syvrc/syvrcboard-v0/PCB/syvrcboard v0.kicad_sch

## KiCad design PCB/syvrcboard v0.kicad_sch (2025-07-31)

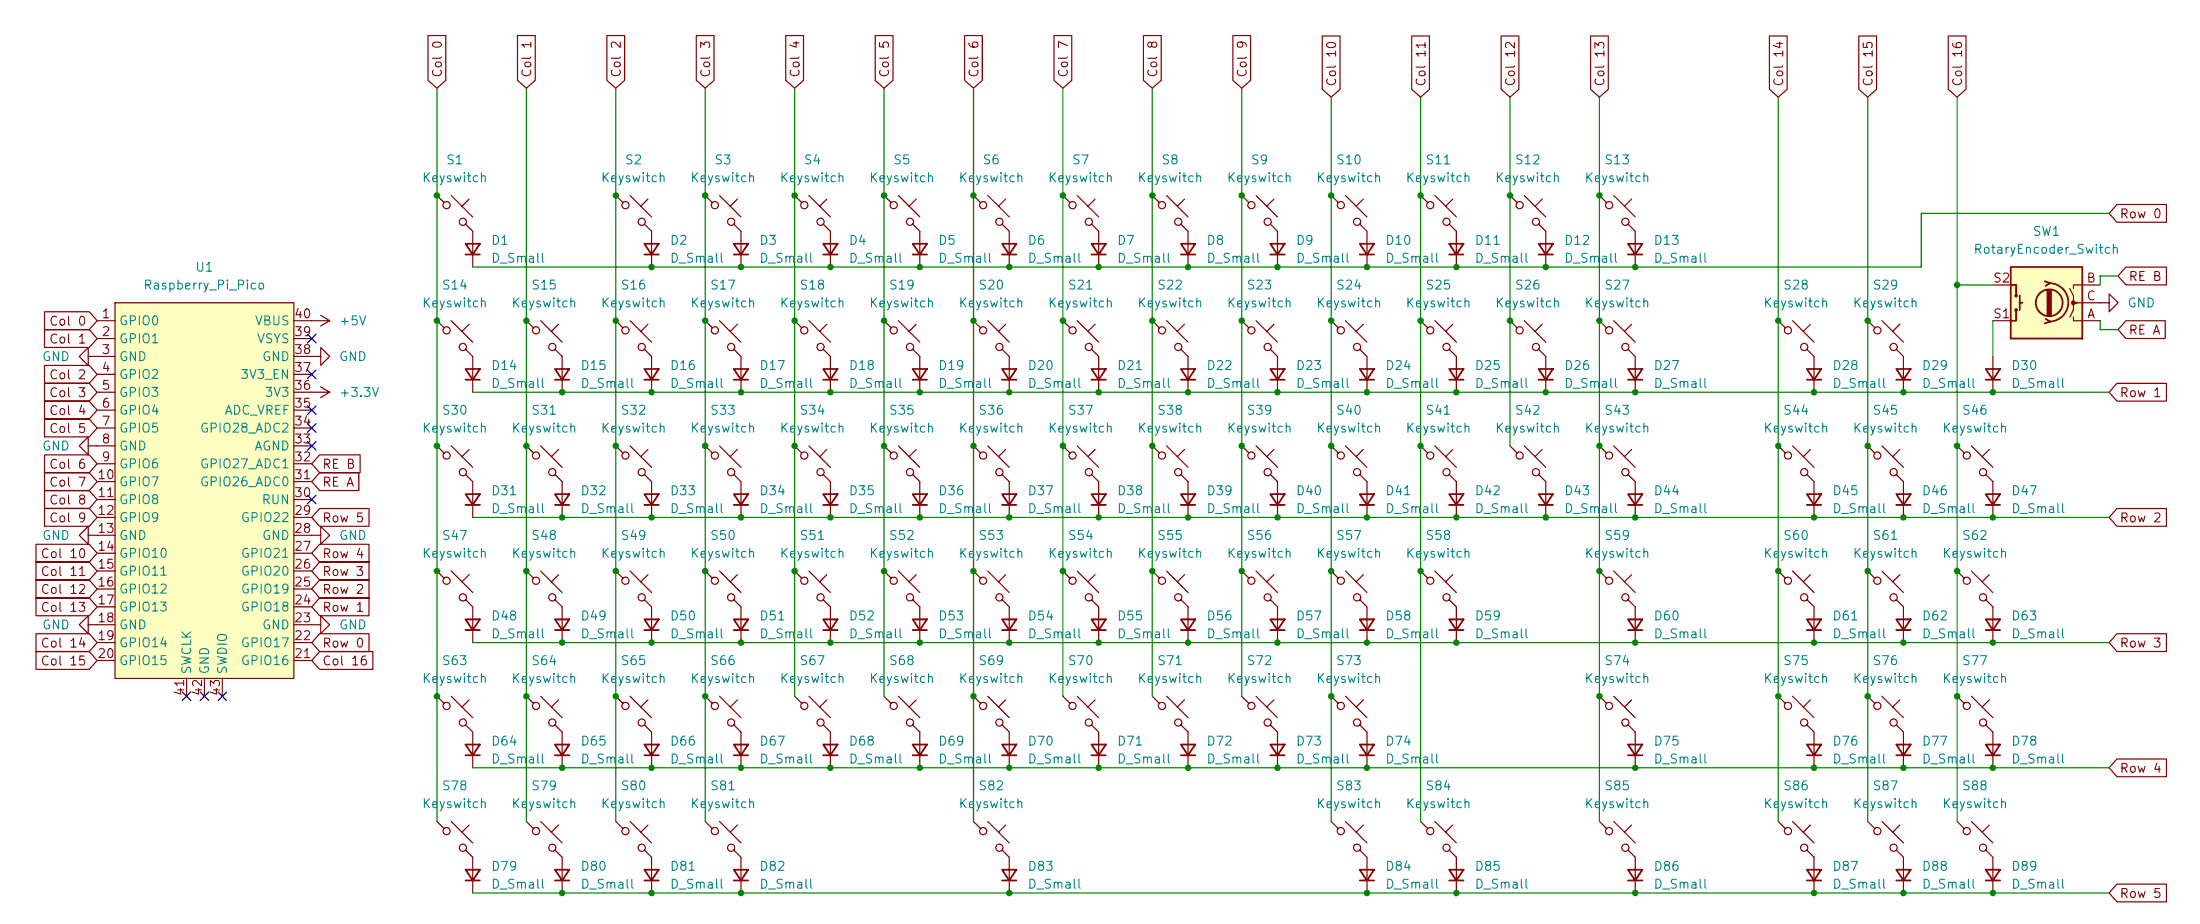
[picture p27: schematic syvrcboard v0.kicad_sch]

Parts:
D1, D2, D3, D4, D5, D6, D7, D8, D9, D10, D11, D12, D13, D14, D15, D16, D17, D18, D19, D20, D21, D22, D23, D24, D25, D26, D27, D28, D29, D30, D31, D32, D33, D34, D35, D36, D37, D38, D39, D40, D41, D42, D43, D44, D45, D46, D47, D48, D49, D50, D51, D52, D53, D54, D55, D56, D57, D58, D59, D60, D61, D62, D63, D64, D65, D66, D67, D68, D69, D70, D71, D72, D73, D74, D75, D76, D77, D78, D79, D80, D81, D82, D83, D84, D85, D86, D87, D88, D89: D_Small; Diode_DO-35
S1, S2, S3, S4, S5, S6, S7, S8, S9, S10, S11, S12, S13, S14, S15, S16, S17, S18, S19, S20, S21, S22, S23, S24, S25, S26, S28, S29, S31, S32, S33, S34, S35, S36, S37, S38, S39, S40, S41, S42, S44, S45, S46, S48, S49, S50, S51, S52, S53, S54, S55, S56, S57, S58, S60, S61, S62, S64, S65, S66, S67, S68, S69, S70, S71, S72, S73, S75, S76, S77, S86, S87, S88: Keyswitch; SW_Cherry_MX_1.00u_PCB
S27: Keyswitch; SW_Cherry_MX_2.00u_PCB
S30, S43: Keyswitch; SW_Cherry_MX_1.50u_PCB
S47: Keyswitch; SW_Cherry_MX_1.75u_PCB
S59, S63: Keyswitch; SW_Cherry_MX_2.25u_PCB
S74: Keyswitch; SW_Cherry_MX_2.75u_PCB
S78, S79, S80, S81, S83, S84, S85: Keyswitch; SW_Cherry_MX_1.25u_PCB
S82: Keyswitch; SW_Cherry_MX_6.25u_PCB
SW1: RotaryEncoder_Switch; RotaryEncoder_Alps_EC11E-Switch_Vertical_H20mm_CircularMoun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
U1: Raspberry_Pi_Pico; RaspberryPi_Pico_Common_THT

Connections:
+3.3V: U1.36 (3V3)
+5V: U1.40 (VBUS)
Col 0: S1.1, S14.1, S30.1, S47.1, S63.1, S78.1, U1.1 (GPIO0)
Col 1: S15.1, S31.1, S48.1, S64.1, S79.1, U1.2 (GPIO1)
Col 2: S2.1, S16.1, S32.1, S49.1, S65.1, S80.1, U1.4 (GPIO2)
Col 3: S3.1, S17.1, S33.1, S50.1, S66.1, S81.1, U1.5 (GPIO3)
Col 4: S4.1, S18.1, S34.1, S51.1, S67.1, U1.6 (GPIO4)
Col 5: S5.1, S19.1, S35.1, S52.1, S68.1, U1.7 (GPIO5)
Col 6: S6.1, S20.1, S36.1, S53.1, S69.1, S82.1, U1.9 (GPIO6)
Col 7: S7.1, S21.1, S37.1, S54.1, S70.1, U1.10 (GPIO7)
Col 8: S8.1, S22.1, S38.1, S55.1, S71.1, U1.11 (GPIO8)
Col 9: S9.1, S23.1, S39.1, S56.1, S72.1, U1.12 (GPIO9)
Col 10: S10.1, S24.1, S40.1, S57.1, S73.1, S83.1, U1.14 (GPIO10)
Col 11: S11.1, S25.1, S41.1, S58.1, S84.1, U1.15 (GPIO11)
Col 12: S12.1, S26.1, S42.1, U1.16 (GPIO12)
Col 13: S13.1, S27.1, S43.1, S59.1, S74.1, S85.1, U1.17 (GPIO13)
Col 14: S28.1, S44.1, S60.1, S75.1, S86.1, U1.19 (GPIO14)
Col 15: S29.1, S45.1, S61.1, S76.1, S87.1, U1.20 (GPIO15)
Col 16: S46.1, S62.1, S77.1, S88.1, SW1.S2, U1.21 (GPIO16)
GND: SW1.C, U1.3 (GND), U1.8 (GND), U1.13 (GND), U1.18 (GND), U1.23 (GND), U1.28 (GND), U1.38 (GND)
unnamed: D1.2 (A), S1.2
unnamed: D2.2 (A), S2.2
unnamed: D3.2 (A), S3.2
unnamed: D4.2 (A), S4.2
unnamed: D5.2 (A), S5.2
unnamed: D6.2 (A), S6.2
unnamed: D7.2 (A), S7.2
unnamed: D8.2 (A), S8.2
unnamed: D9.2 (A), S9.2
unnamed: D10.2 (A), S10.2
unnamed: D11.2 (A), S11.2
unnamed: D12.2 (A), S12.2
unnamed: D13.2 (A), S13.2
unnamed: D14.2 (A), S14.2
unnamed: D15.2 (A), S15.2
unnamed: D16.2 (A), S16.2
unnamed: D17.2 (A), S17.2
unnamed: D18.2 (A), S18.2
unnamed: D19.2 (A), S19.2
unnamed: D20.2 (A), S20.2
unnamed: D21.2 (A), S21.2
unnamed: D22.2 (A), S22.2
unnamed: D23.2 (A), S23.2
unnamed: D24.2 (A), S24.2
unnamed: D25.2 (A), S25.2
unnamed: D26.2 (A), S26.2
unnamed: D27.2 (A), S27.2
unnamed: D28.2 (A), S28.2
unnamed: D29.2 (A), S29.2
unnamed: D30.2 (A), SW1.S1
unnamed: D31.2 (A), S30.2
unnamed: D32.2 (A), S31.2
unnamed: D33.2 (A), S32.2
unnamed: D34.2 (A), S33.2
unnamed: D35.2 (A), S34.2
unnamed: D36.2 (A), S35.2
unnamed: D37.2 (A), S36.2
unnamed: D38.2 (A), S37.2
unnamed: D39.2 (A), S38.2
unnamed: D40.2 (A), S39.2
unnamed: D41.2 (A), S40.2
unnamed: D42.2 (A), S41.2
unnamed: D43.2 (A), S42.2
unnamed: D44.2 (A), S43.2
unnamed: D45.2 (A), S44.2
unnamed: D46.2 (A), S45.2
unnamed: D47.2 (A), S46.2
unnamed: D48.2 (A), S47.2
unnamed: D49.2 (A), S48.2
unnamed: D50.2 (A), S49.2
unnamed: D51.2 (A), S50.2
unnamed: D52.2 (A), S51.2
unnamed: D53.2 (A), S52.2
unnamed: D54.2 (A), S53.2
unnamed: D55.2 (A), S54.2
unnamed: D56.2 (A), S55.2
unnamed: D57.2 (A), S56.2
unnamed: D58.2 (A), S57.2
unnamed: D59.2 (A), S58.2
unnamed: D60.2 (A), S59.2
unnamed: D61.2 (A), S60.2
unnamed: D62.2 (A), S61.2
unnamed: D63.2 (A), S62.2
unnamed: D64.2 (A), S63.2
unnamed: D65.2 (A), S64.2
unnamed: D66.2 (A), S65.2
unnamed: D67.2 (A), S66.2
unnamed: D68.2 (A), S67.2
unnamed: D69.2 (A), S68.2
unnamed: D70.2 (A), S69.2
unnamed: D71.2 (A), S70.2
unnamed: D72.2 (A), S71.2
unnamed: D73.2 (A), S72.2
unnamed: D74.2 (A), S73.2
unnamed: D75.2 (A), S74.2
unnamed: D76.2 (A), S75.2
unnamed: D77.2 (A), S76.2
unnamed: D78.2 (A), S77.2
unnamed: D79.2 (A), S78.2
unnamed: D80.2 (A), S79.2
unnamed: D81.2 (A), S80.2
unnamed: D82.2 (A), S81.2
unnamed: D83.2 (A), S82.2
unnamed: D84.2 (A), S83.2
unnamed: D85.2 (A), S84.2
unnamed: D86.2 (A), S85.2
unnamed: D87.2 (A), S86.2
unnamed: D88.2 (A), S87.2
unnamed: D89.2 (A), S88.2
RE A: SW1.A, U1.31 (GPIO26_ADC0)
RE B: SW1.B, U1.32 (GPIO27_ADC1)
Row 0: D1.1 (K), D2.1 (K), D3.1 (K), D4.1 (K), D5.1 (K), D6.1 (K), D7.1 (K), D8.1 (K), D9.1 (K), D10.1 (K), D11.1 (K), D12.1 (K), D13.1 (K), U1.22 (GPIO17)
Row 1: D14.1 (K), D15.1 (K), D16.1 (K), D17.1 (K), D18.1 (K), D19.1 (K), D20.1 (K), D21.1 (K), D22.1 (K), D23.1 (K), D24.1 (K), D25.1 (K), D26.1 (K), D27.1 (K), D28.1 (K), D29.1 (K), D30.1 (K), U1.24 (GPIO18)
Row 2: D31.1 (K), D32.1 (K), D33.1 (K), D34.1 (K), D35.1 (K), D36.1 (K), D37.1 (K), D38.1 (K), D39.1 (K), D40.1 (K), D41.1 (K), D42.1 (K), D43.1 (K), D44.1 (K), D45.1 (K), D46.1 (K), D47.1 (K), U1.25 (GPIO19)
Row 3: D48.1 (K), D49.1 (K), D50.1 (K), D51.1 (K), D52.1 (K), D53.1 (K), D54.1 (K), D55.1 (K), D56.1 (K), D57.1 (K), D58.1 (K), D59.1 (K), D60.1 (K), D61.1 (K), D62.1 (K), D63.1 (K), U1.26 (GPIO20)
Row 4: D64.1 (K), D65.1 (K), D66.1 (K), D67.1 (K), D68.1 (K), D69.1 (K), D70.1 (K), D71.1 (K), D72.1 (K), D73.1 (K), D74.1 (K), D75.1 (K), D76.1 (K), D77.1 (K), D78.1 (K), U1.27 (GPIO21)
Row 5: D79.1 (K), D80.1 (K), D81.1 (K), D82.1 (K), D83.1 (K), D84.1 (K), D85.1 (K), D86.1 (K), D87.1 (K), D88.1 (K), D89.1 (K), U1.29 (GPIO22)
